weteor/Kong/pcb/choc/kongChoc.kicad_sch

## KiCad design pcb/choc/kongChoc.kicad_sch (2023-03-22)

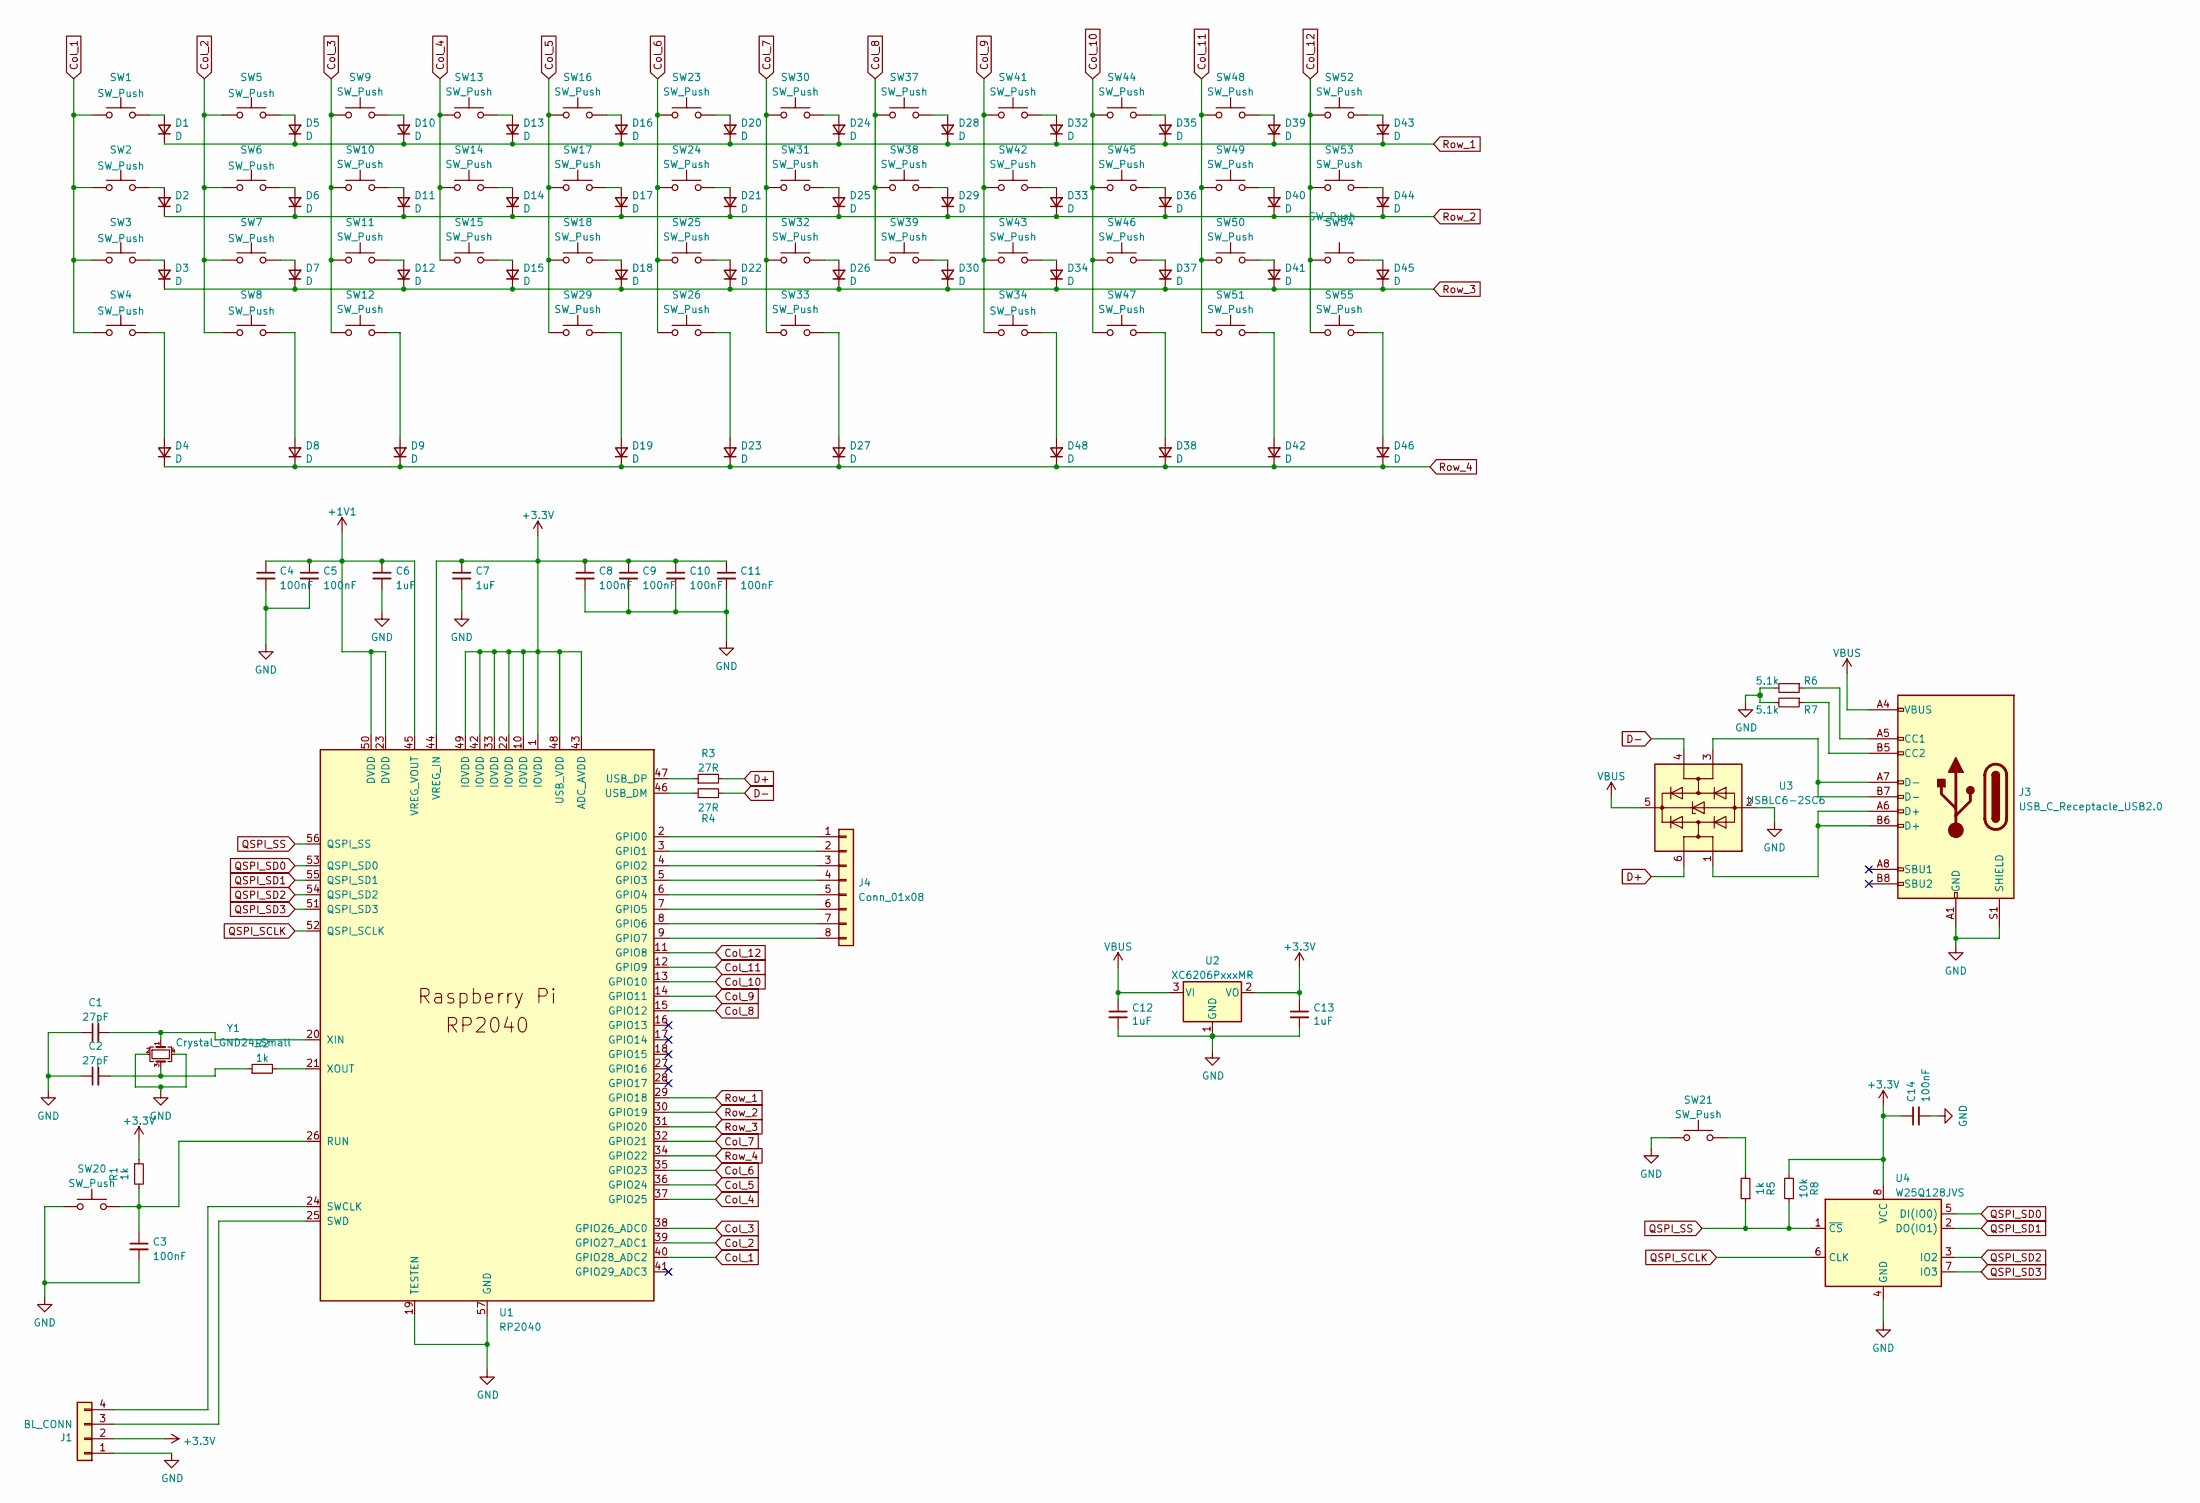
[picture p16: schematic kongChoc.kicad_sch]

Parts:
C1, C2: 27pF; C_0402_HandSolder
C3, C4, C5, C8, C9, C10, C11, C14: 100nF; C_0402_HandSolder
C6, C7, C12, C13: 1uF; C_0402_HandSolder
D1, D2, D3, D4, D5, D6, D7, D8, D9, D10, D11, D12, D13, D14, D15, D16, D17, D18, D19, D20, D21, D22, D23, D24, D25, D26, D27, D28, D29, D30, D32, D33, D34, D35, D36, D37, D38, D39, D40, D41, D42, D43, D44, D45, D46, D48: D; D_SOD-123
J1: BL_CONN; PinHeader_1x04_P2.54mm_Vertical
J3: USB_C_Receptacle_USB2.0; USB-C-12-Pin-MidMount
J4: Conn_01x08; PinHeader_1x08_P2.54mm_Vertical
R1, R2, R5: 1k; R_0402_HandSolder
R3, R4: 27R; R_0402_HandSolder
R6, R7: 5.1k; R_0402_HandSolder
R8: 10k; R_0402_HandSolder
SW1, SW2, SW3, SW4, SW5, SW6, SW7, SW8, SW9, SW10, SW11, SW12, SW13, SW14, SW15, SW16, SW17, SW18, SW23, SW24, SW25, SW26, SW30, SW31, SW32, SW33, SW37, SW38, SW39, SW41, SW42, SW43, SW44, SW45, SW46, SW47, SW48, SW49, SW50, SW51, SW52, SW53, SW54, SW55: SW_Push; ChocV1_V2_Hotswap
SW20, SW21: SW_Push; Micro_Push_Button_3x6x2.5mm
SW29, SW34: SW_Push; ChocV1_V2_Hotswap_2u
U1: RP2040; RP2040-QFN-56
U2: XC6206PxxxMR; SOT-23
U3: USBLC6-2SC6; SOT-23-6
U4: W25Q128JVS; WSON-8-1EP_6x5mm_P1.27mm_EP3.4x4.3mm
Y1: Crystal_GND24_Small; Crystal_SMD_2520-4Pin_2.5x2.0mm

Connections:
+1V1: C4.1, C5.1, C6.1, U1.23 (DVDD), U1.45 (VREG_VOUT), U1.50 (DVDD)
+3.3V: C7.1, C8.1, C9.1, C10.1, C11.1, C13.1, C14.1, J1.2, R1.1, R8.2, U1.1 (IOVDD), U1.10 (IOVDD), U1.22 (IOVDD), U1.33 (IOVDD), U1.42 (IOVDD), U1.43 (ADC_AVDD), U1.44 (VREG_IN), U1.48 (USB_VDD), U1.49 (IOVDD), U2.2 (VO), U4.8 (VCC)
Col_1: SW1.1, SW2.1, SW3.1, SW4.1, U1.40 (GPIO28_ADC2)
Col_2: SW5.1, SW6.1, SW7.1, SW8.1, U1.39 (GPIO27_ADC1)
Col_3: SW9.1, SW10.1, SW11.1, SW12.1, U1.38 (GPIO26_ADC0)
Col_4: SW13.1, SW14.1, SW15.1, U1.37 (GPIO25)
Col_5: SW16.1, SW17.1, SW18.1, SW29.1, U1.36 (GPIO24)
Col_6: SW23.1, SW24.1, SW25.1, SW26.1, U1.35 (GPIO23)
Col_7: SW30.1, SW31.1, SW32.1, SW33.1, U1.32 (GPIO21)
Col_8: SW37.1, SW38.1, SW39.1, U1.15 (GPIO12)
Col_9: SW34.1, SW41.1, SW42.1, SW43.1, U1.14 (GPIO11)
Col_10: SW44.1, SW45.1, SW46.1, SW47.1, U1.13 (GPIO10)
Col_11: SW48.1, SW49.1, SW50.1, SW51.1, U1.12 (GPIO9)
Col_12: SW52.1, SW53.1, SW54.1, SW55.1, U1.11 (GPIO8)
D+: R3.2, U3.6 (I/O1)
D-: R4.2, U3.4 (I/O2)
GND: C1.1, C2.1, C3.2, C4.2, C5.2, C6.2, C7.2, C8.2, C9.2, C10.2, C11.2, C12.2, C13.2, C14.2, J1.1, J3.A1 (GND), J3.A12 (GND), J3.B1 (GND), J3.B12 (GND), J3.S1 (SHIELD), R6.2, R7.2, SW20.1, SW21.1, U1.19 (TESTEN), U1.57 (GND), U2.1 (GND), U3.2 (GND), U4.4 (GND), Y1.2, Y1.4
unnamed: C1.2, U1.20 (XIN), Y1.1
unnamed: C2.2, R2.1, Y1.3
unnamed: C3.1, R1.2, SW20.2, U1.26 (RUN)
unnamed: D1.2 (A), SW1.2
unnamed: D2.2 (A), SW2.2
unnamed: D3.2 (A), SW3.2
unnamed: D4.2 (A), SW4.2
unnamed: D5.2 (A), SW5.2
unnamed: D6.2 (A), SW6.2
unnamed: D7.2 (A), SW7.2
unnamed: D8.2 (A), SW8.2
unnamed: D9.2 (A), SW12.2
unnamed: D10.2 (A), SW9.2
unnamed: D11.2 (A), SW10.2
unnamed: D12.2 (A), SW11.2
unnamed: D13.2 (A), SW13.2
unnamed: D14.2 (A), SW14.2
unnamed: D15.2 (A), SW15.2
unnamed: D16.2 (A), SW16.2
unnamed: D17.2 (A), SW17.2
unnamed: D18.2 (A), SW18.2
unnamed: D19.2 (A), SW29.2
unnamed: D20.2 (A), SW23.2
unnamed: D21.2 (A), SW24.2
unnamed: D22.2 (A), SW25.2
unnamed: D23.2 (A), SW26.2
unnamed: D24.2 (A), SW30.2
unnamed: D25.2 (A), SW31.2
unnamed: D26.2 (A), SW32.2
unnamed: D27.2 (A), SW33.2
unnamed: D28.2 (A), SW37.2
unnamed: D29.2 (A), SW38.2
unnamed: D30.2 (A), SW39.2
unnamed: D32.2 (A), SW41.2
unnamed: D33.2 (A), SW42.2
unnamed: D34.2 (A), SW43.2
unnamed: D35.2 (A), SW44.2
unnamed: D36.2 (A), SW45.2
unnamed: D37.2 (A), SW46.2
unnamed: D38.2 (A), SW47.2
unnamed: D39.2 (A), SW48.2
unnamed: D40.2 (A), SW49.2
unnamed: D41.2 (A), SW50.2
unnamed: D42.2 (A), SW51.2
unnamed: D43.2 (A), SW52.2
unnamed: D44.2 (A), SW53.2
unnamed: D45.2 (A), SW54.2
unnamed: D46.2 (A), SW55.2
unnamed: D48.2 (A), SW34.2
unnamed: J1.3, U1.25 (SWD)
unnamed: J1.4, U1.24 (SWCLK)
unnamed: J3.A5 (CC1), R6.1
unnamed: J3.A6 (D+), J3.B6 (D+), U3.1 (I/O1)
unnamed: J3.A7 (D-), J3.B7 (D-), U3.3 (I/O2)
unnamed: J3.B5 (CC2), R7.1
unnamed: J4.1, U1.2 (GPIO0)
unnamed: J4.2, U1.3 (GPIO1)
unnamed: J4.3, U1.4 (GPIO2)
unnamed: J4.4, U1.5 (GPIO3)
unnamed: J4.5, U1.6 (GPIO4)
unnamed: J4.6, U1.7 (GPIO5)
unnamed: J4.7, U1.8 (GPIO6)
unnamed: J4.8, U1.9 (GPIO7)
unnamed: R2.2, U1.21 (XOUT)
unnamed: R3.1, U1.47 (USB_DP)
unnamed: R4.1, U1.46 (USB_DM)
unnamed: R5.2, SW21.2
QSPI_SCLK: U1.52 (QSPI_SCLK), U4.6 (CLK)
QSPI_SD0: U1.53 (QSPI_SD0), U4.5 (DI(IO0))
QSPI_SD1: U1.55 (QSPI_SD1), U4.2 (DO(IO1))
QSPI_SD2: U1.54 (QSPI_SD2), U4.3 (IO2)
QSPI_SD3: U1.51 (QSPI_SD3), U4.7 (IO3)
QSPI_SS: R5.1, R8.1, U1.56 (QSPI_SS), U4.1 (~CS)
Row_1: D1.1 (K), D5.1 (K), D10.1 (K), D13.1 (K), D16.1 (K), D20.1 (K), D24.1 (K), D28.1 (K), D32.1 (K), D35.1 (K), D39.1 (K), D43.1 (K), U1.29 (GPIO18)
Row_2: D2.1 (K), D6.1 (K), D11.1 (K), D14.1 (K), D17.1 (K), D21.1 (K), D25.1 (K), D29.1 (K), D33.1 (K), D36.1 (K), D40.1 (K), D44.1 (K), U1.30 (GPIO19)
Row_3: D3.1 (K), D7.1 (K), D12.1 (K), D15.1 (K), D18.1 (K), D22.1 (K), D26.1 (K), D30.1 (K), D34.1 (K), D37.1 (K), D41.1 (K), D45.1 (K), U1.31 (GPIO20)
Row_4: D4.1 (K), D8.1 (K), D9.1 (K), D19.1 (K), D23.1 (K), D27.1 (K), D38.1 (K), D42.1 (K), D46.1 (K), D48.1 (K), U1.34 (GPIO22)
VBUS: C12.1, J3.A4 (VBUS), J3.A9 (VBUS), J3.B4 (VBUS), J3.B9 (VBUS), U2.3 (VI), U3.5 (VBUS)
