weteor/Kong/pcb/mx/kongMX.kicad_sch

## KiCad design pcb/mx/kongMX.kicad_sch (2023-02-16)

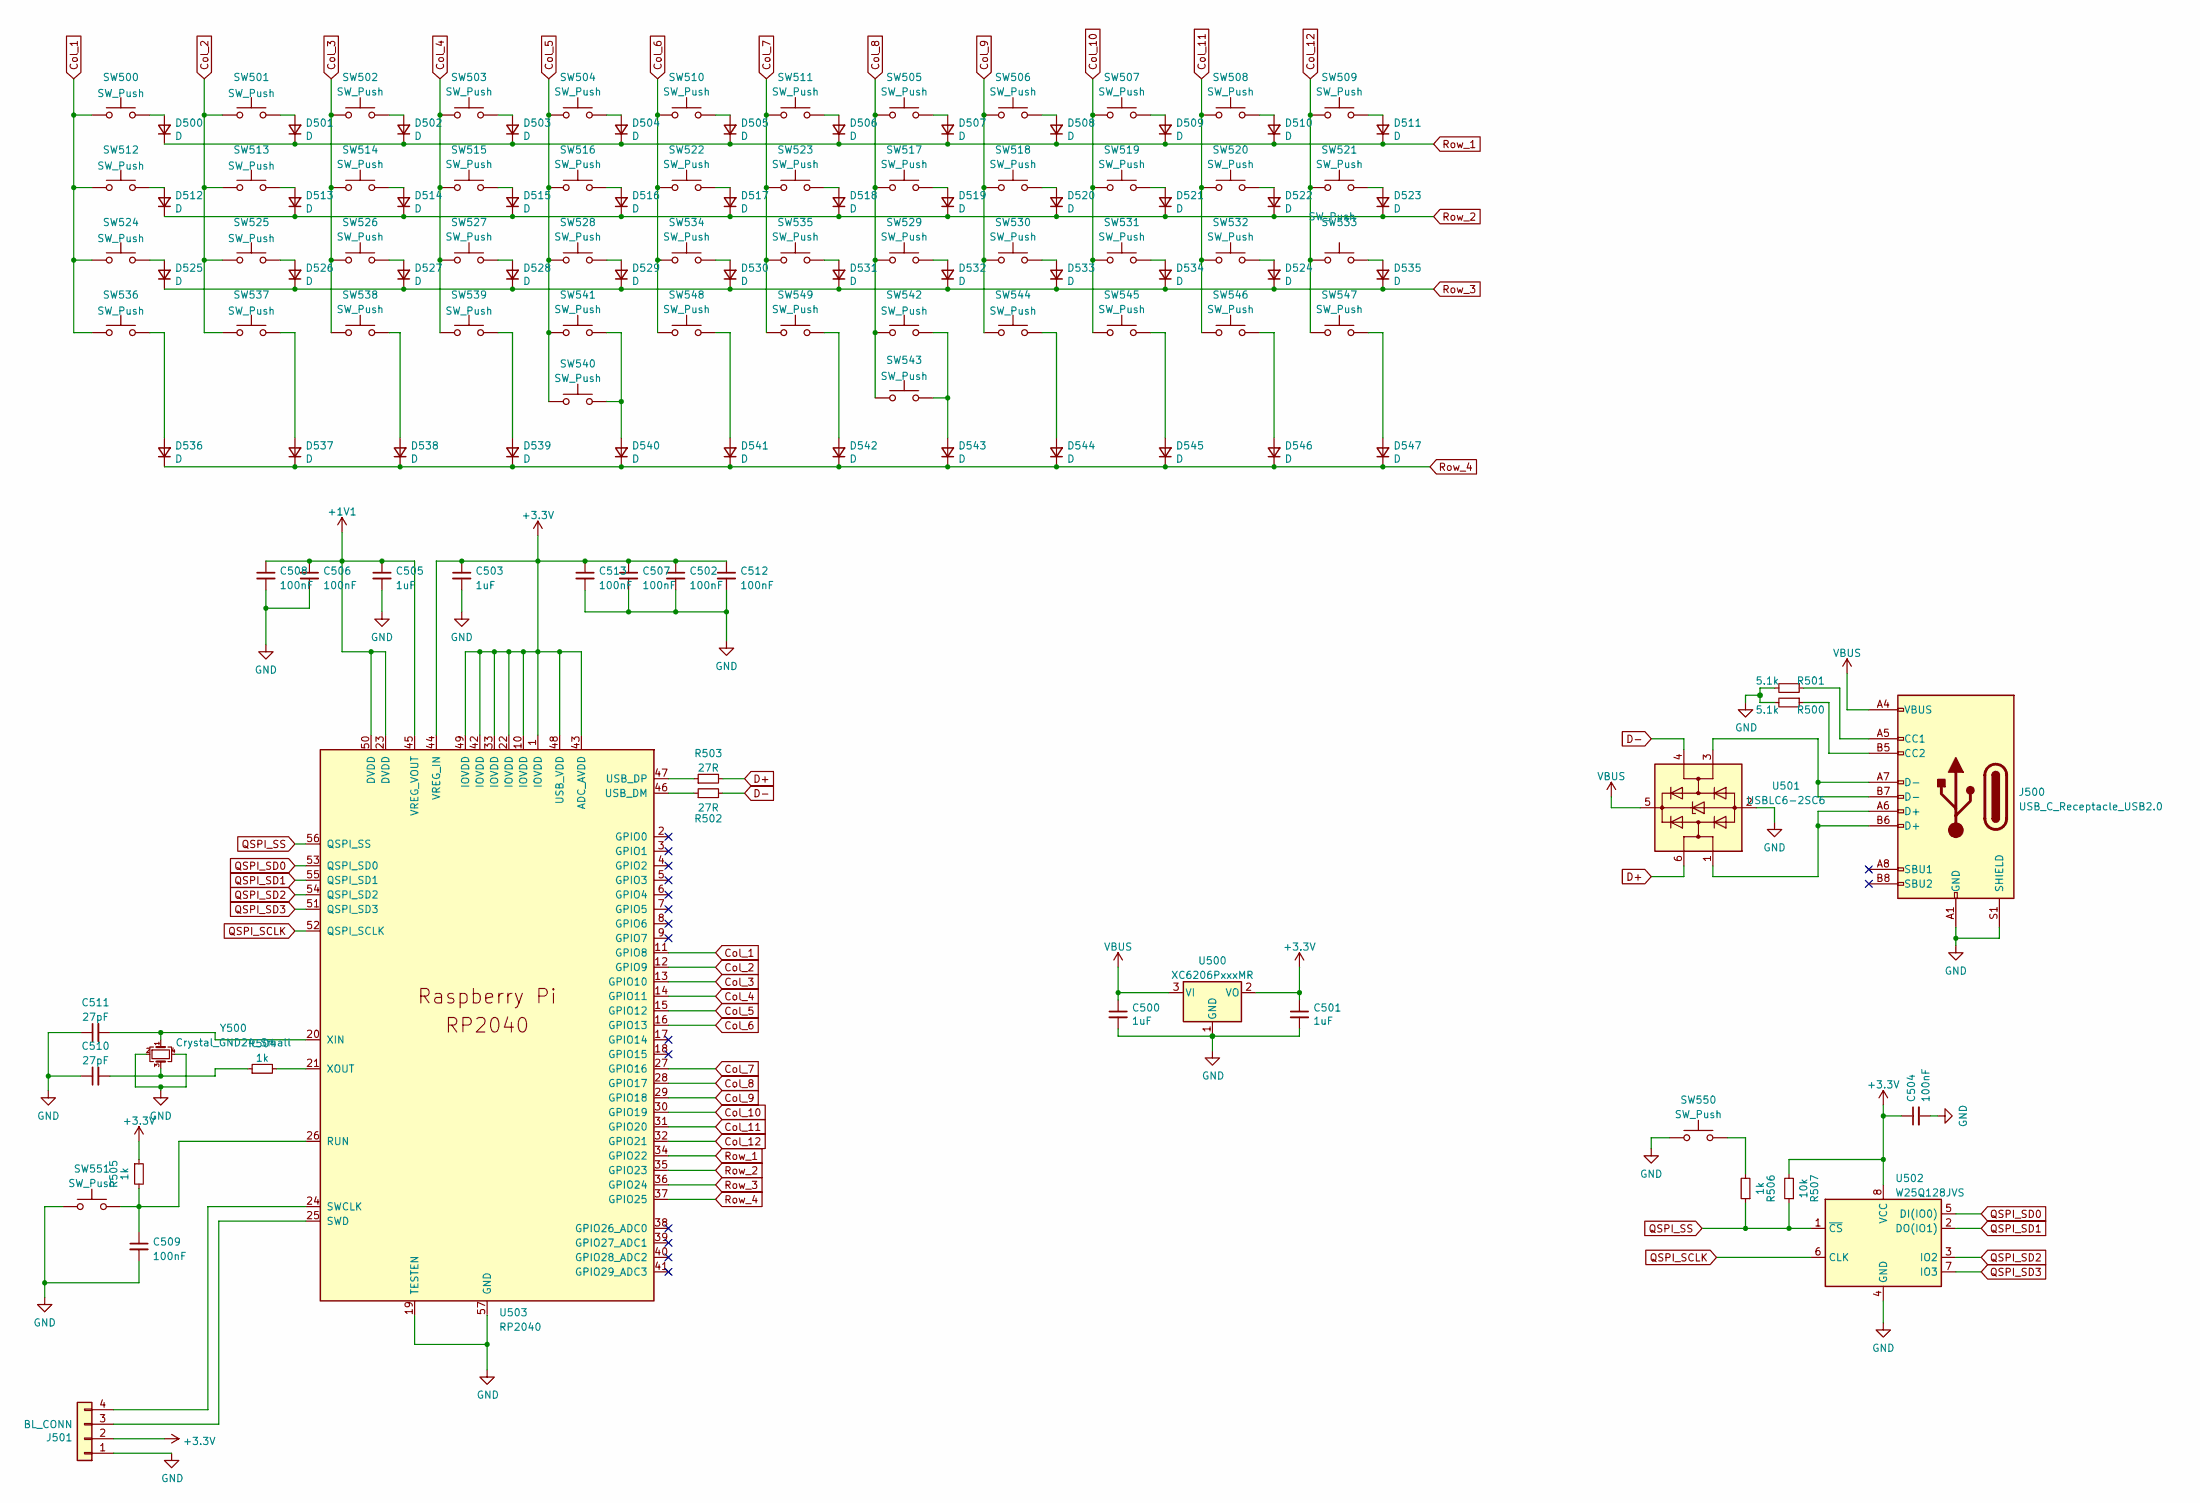
[picture p17: schematic kongMX.kicad_sch]

Parts:
C500, C501, C503, C505: 1uF; C_0402_1005Metric
C502, C504, C506, C507, C508, C509, C512, C513: 100nF; C_0402_1005Metric
C510, C511: 27pF; C_0402_1005Metric
D500, D501, D502, D503, D504, D505, D506, D507, D508, D509, D510, D511, D512, D513, D514, D515, D516, D517, D518, D519, D520, D521, D522, D523, D524, D525, D526, D527, D528, D529, D530, D531, D532, D533, D534, D535, D536, D537, D538, D539, D540, D541, D542, D543, D544, D545, D546, D547: D; D_SOD-123
J500: USB_C_Receptacle_USB2.0; USB-C-31-M-14_C22
J501: BL_CONN; PinHeader_1x04_P2.54mm_Vertical
R500, R501: 5.1k; R_0402_1005Metric
R502, R503: 27R; R_0402_1005Metric
R504, R505, R506: 1k; R_0402_1005Metric
R507: 10k; R_0402_1005Metric
SW500, SW501, SW502, SW503, SW504, SW505, SW506, SW507, SW508, SW509, SW510, SW511, SW512, SW513, SW514, SW515, SW516, SW517, SW518, SW519, SW520, SW521, SW522, SW523, SW524, SW525, SW526, SW527, SW528, SW529, SW530, SW531, SW532, SW533, SW534, SW535, SW536, SW537, SW538, SW545, SW546, SW547, SW548, SW549: SW_Push; CherryMX_Hotswap
SW539, SW541, SW542, SW544: SW_Push; CherryMX_Hotswap_3u_stabs
SW540, SW543: SW_Push; CherryMX_Hotswap_2u_stabs
SW550, SW551: SW_Push; Micro_Push_Button_3x6x2.5mm
U500: XC6206PxxxMR; SOT-23
U501: USBLC6-2SC6; SOT-23-6
U502: W25Q128JVS; SOIC-8_5.23x5.23mm_P1.27mm
U503: RP2040; RP2040-QFN-56
Y500: Crystal_GND24_Small; Crystal_SMD_2520-4Pin_2.5x2.0mm

Connections:
+1V1: C505.1, C506.1, C508.1, U503.23 (DVDD), U503.45 (VREG_VOUT), U503.50 (DVDD)
+3.3V: C501.1, C502.1, C503.1, C504.1, C507.1, C512.1, C513.1, J501.2, R505.1, R507.2, U500.2 (VO), U502.8 (VCC), U503.1 (IOVDD), U503.10 (IOVDD), U503.22 (IOVDD), U503.33 (IOVDD), U503.42 (IOVDD), U503.43 (ADC_AVDD), U503.44 (VREG_IN), U503.48 (USB_VDD), U503.49 (IOVDD)
Col_1: SW500.1, SW512.1, SW524.1, SW536.1, U503.11 (GPIO8)
Col_2: SW501.1, SW513.1, SW525.1, SW537.1, U503.12 (GPIO9)
Col_3: SW502.1, SW514.1, SW526.1, SW538.1, U503.13 (GPIO10)
Col_4: SW503.1, SW515.1, SW527.1, SW539.1, U503.14 (GPIO11)
Col_5: SW504.1, SW516.1, SW528.1, SW540.1, SW541.1, U503.15 (GPIO12)
Col_6: SW510.1, SW522.1, SW534.1, SW548.1, U503.16 (GPIO13)
Col_7: SW511.1, SW523.1, SW535.1, SW549.1, U503.27 (GPIO16)
Col_8: SW505.1, SW517.1, SW529.1, SW542.1, SW543.1, U503.28 (GPIO17)
Col_9: SW506.1, SW518.1, SW530.1, SW544.1, U503.29 (GPIO18)
Col_10: SW507.1, SW519.1, SW531.1, SW545.1, U503.30 (GPIO19)
Col_11: SW508.1, SW520.1, SW532.1, SW546.1, U503.31 (GPIO20)
Col_12: SW509.1, SW521.1, SW533.1, SW547.1, U503.32 (GPIO21)
D+: R503.2, U501.6 (I/O1)
D-: R502.2, U501.4 (I/O2)
GND: C500.2, C501.2, C502.2, C503.2, C504.2, C505.2, C506.2, C507.2, C508.2, C509.2, C510.1, C511.1, C512.2, C513.2, J500.A1 (GND), J500.A12 (GND), J500.B1 (GND), J500.B12 (GND), J500.S1 (SHIELD), J501.1, R500.2, R501.2, SW550.1, SW551.1, U500.1 (GND), U501.2 (GND), U502.4 (GND), U503.19 (TESTEN), U503.57 (GND), Y500.2, Y500.4
unnamed: C509.1, R505.2, SW551.2, U503.26 (RUN)
unnamed: C510.2, R504.1, Y500.3
unnamed: C511.2, U503.20 (XIN), Y500.1
unnamed: D500.2 (A), SW500.2
unnamed: D501.2 (A), SW501.2
unnamed: D502.2 (A), SW502.2
unnamed: D503.2 (A), SW503.2
unnamed: D504.2 (A), SW504.2
unnamed: D505.2 (A), SW510.2
unnamed: D506.2 (A), SW511.2
unnamed: D507.2 (A), SW505.2
unnamed: D508.2 (A), SW506.2
unnamed: D509.2 (A), SW507.2
unnamed: D510.2 (A), SW508.2
unnamed: D511.2 (A), SW509.2
unnamed: D512.2 (A), SW512.2
unnamed: D513.2 (A), SW513.2
unnamed: D514.2 (A), SW514.2
unnamed: D515.2 (A), SW515.2
unnamed: D516.2 (A), SW516.2
unnamed: D517.2 (A), SW522.2
unnamed: D518.2 (A), SW523.2
unnamed: D519.2 (A), SW517.2
unnamed: D520.2 (A), SW518.2
unnamed: D521.2 (A), SW519.2
unnamed: D522.2 (A), SW520.2
unnamed: D523.2 (A), SW521.2
unnamed: D524.2 (A), SW532.2
unnamed: D525.2 (A), SW524.2
unnamed: D526.2 (A), SW525.2
unnamed: D527.2 (A), SW526.2
unnamed: D528.2 (A), SW527.2
unnamed: D529.2 (A), SW528.2
unnamed: D530.2 (A), SW534.2
unnamed: D531.2 (A), SW535.2
unnamed: D532.2 (A), SW529.2
unnamed: D533.2 (A), SW530.2
unnamed: D534.2 (A), SW531.2
unnamed: D535.2 (A), SW533.2
unnamed: D536.2 (A), SW536.2
unnamed: D537.2 (A), SW537.2
unnamed: D538.2 (A), SW538.2
unnamed: D539.2 (A), SW539.2
unnamed: D540.2 (A), SW540.2, SW541.2
unnamed: D541.2 (A), SW548.2
unnamed: D542.2 (A), SW549.2
unnamed: D543.2 (A), SW542.2, SW543.2
unnamed: D544.2 (A), SW544.2
unnamed: D545.2 (A), SW545.2
unnamed: D546.2 (A), SW546.2
unnamed: D547.2 (A), SW547.2
unnamed: J500.A5 (CC1), R501.1
unnamed: J500.A6 (D+), J500.B6 (D+), U501.1 (I/O1)
unnamed: J500.A7 (D-), J500.B7 (D-), U501.3 (I/O2)
unnamed: J500.B5 (CC2), R500.1
unnamed: J501.3, U503.25 (SWD)
unnamed: J501.4, U503.24 (SWCLK)
unnamed: R502.1, U503.46 (USB_DM)
unnamed: R503.1, U503.47 (USB_DP)
unnamed: R504.2, U503.21 (XOUT)
unnamed: R506.2, SW550.2
QSPI_SCLK: U502.6 (CLK), U503.52 (QSPI_SCLK)
QSPI_SD0: U502.5 (DI(IO0)), U503.53 (QSPI_SD0)
QSPI_SD1: U502.2 (DO(IO1)), U503.55 (QSPI_SD1)
QSPI_SD2: U502.3 (IO2), U503.54 (QSPI_SD2)
QSPI_SD3: U502.7 (IO3), U503.51 (QSPI_SD3)
QSPI_SS: R506.1, R507.1, U502.1 (~CS), U503.56 (QSPI_SS)
Row_1: D500.1 (K), D501.1 (K), D502.1 (K), D503.1 (K), D504.1 (K), D505.1 (K), D506.1 (K), D507.1 (K), D508.1 (K), D509.1 (K), D510.1 (K), D511.1 (K), U503.34 (GPIO22)
Row_2: D512.1 (K), D513.1 (K), D514.1 (K), D515.1 (K), D516.1 (K), D517.1 (K), D518.1 (K), D519.1 (K), D520.1 (K), D521.1 (K), D522.1 (K), D523.1 (K), U503.35 (GPIO23)
Row_3: D524.1 (K), D525.1 (K), D526.1 (K), D527.1 (K), D528.1 (K), D529.1 (K), D530.1 (K), D531.1 (K), D532.1 (K), D533.1 (K), D534.1 (K), D535.1 (K), U503.36 (GPIO24)
Row_4: D536.1 (K), D537.1 (K), D538.1 (K), D539.1 (K), D540.1 (K), D541.1 (K), D542.1 (K), D543.1 (K), D544.1 (K), D545.1 (K), D546.1 (K), D547.1 (K), U503.37 (GPIO25)
VBUS: C500.1, J500.A4 (VBUS), J500.A9 (VBUS), J500.B4 (VBUS), J500.B9 (VBUS), U500.3 (VI), U501.5 (VBUS)
